proudcloud/clouduino/docs/images/preferences.png

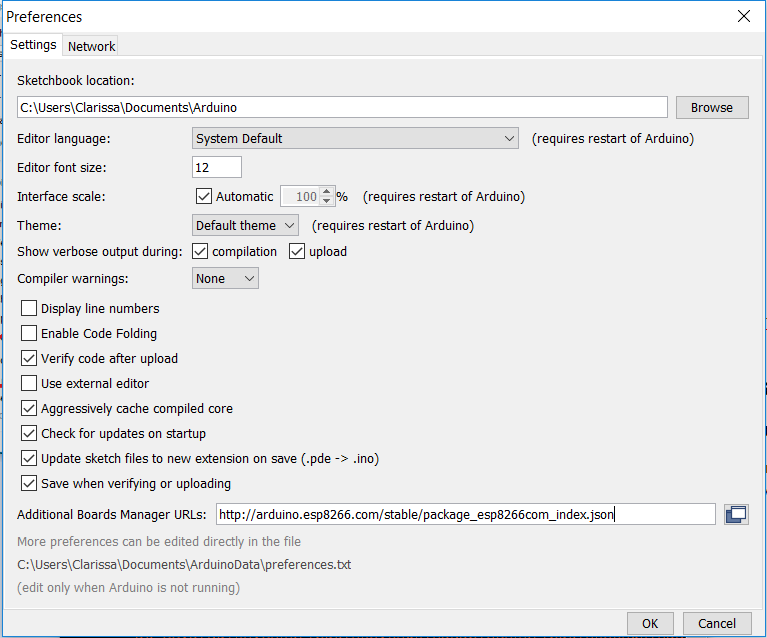
docs/images/preferences.png
