proudcloud/clouduino/example/Webserver_example/Clouduino_Webserver_LEDs_fritzing_Breadboard.PNG

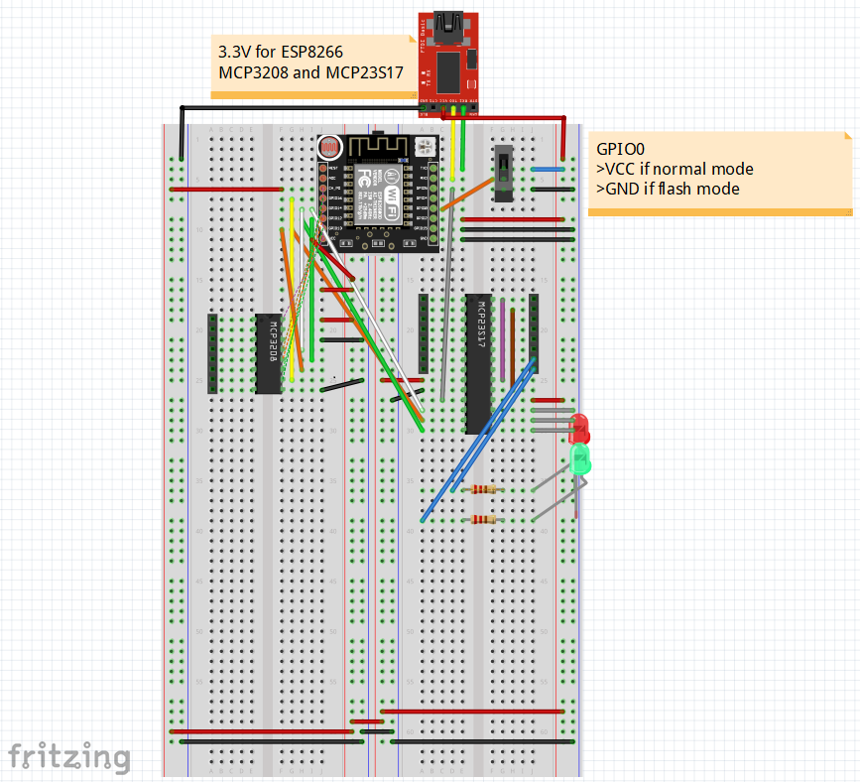
example/Webserver_example/Clouduino_Webserver_LEDs_fritzing_Breadboard.PNG
