proudcloud/clouduino/example/Webserver_example/Clouduino_Webserver_LEDs_fritzing_Schem.PNG

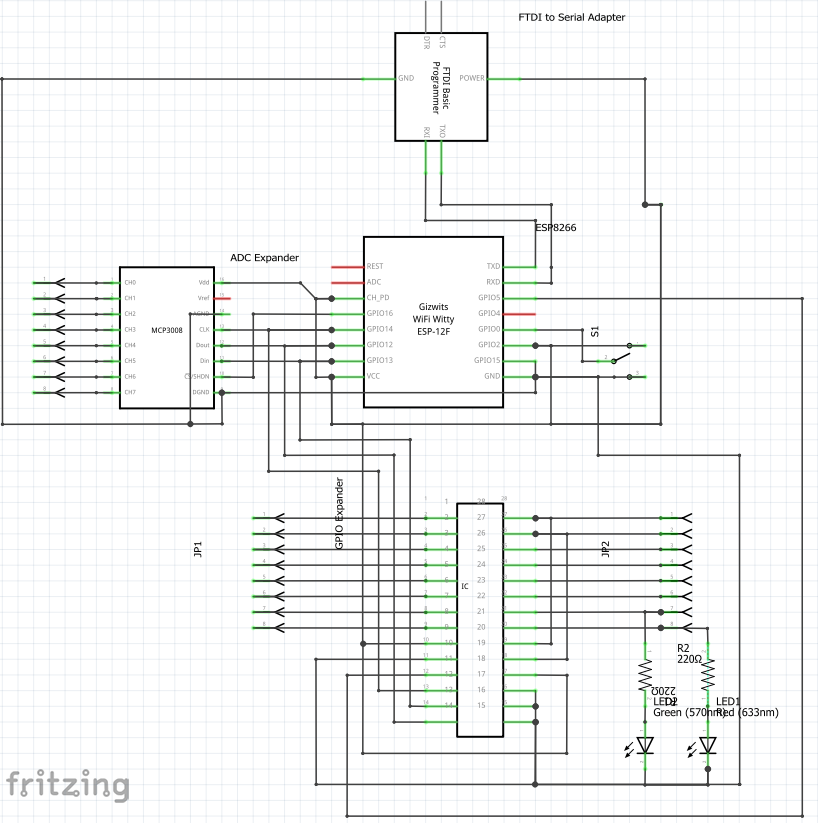
example/Webserver_example/Clouduino_Webserver_LEDs_fritzing_Schem.PNG
