proudcloud/clouduino/example/ADC_example/ADC_test_LDR fritzing_Schem.PNG

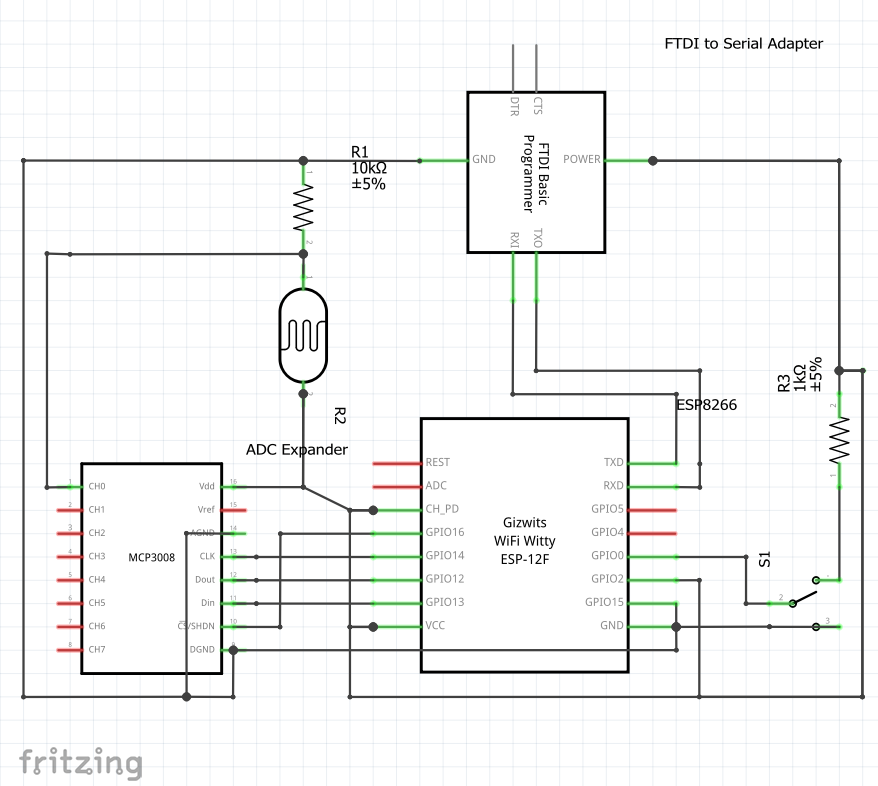
example/ADC_example/ADC_test_LDR fritzing_Schem.PNG
