proudcloud/clouduino/example/ADC_example/ADC_test_LDR/ADC_test_LDR.ino

/**
 * Basic ADC reading example.
 * - connects to ADC
 * - reads value from channel
 * - converts value to analog voltage
 */

#include <SPI.h>
#include <Mcp3208.h>

#define SPI_CS    	16 		   // SPI slave select: GPIO16 pin of ESP8266
#define ADC_VREF    3300     // 3.3V Vref
#define ADC_CLK     1600000  // SPI clock 1.6MHz


MCP3208 adc(ADC_VREF, SPI_CS);

void setup() {

  // configure PIN mode
  pinMode(SPI_CS, OUTPUT);

  // set initial PIN state
  digitalWrite(SPI_CS, HIGH);

  // initialize serial
  Serial.begin(115200);     

  // initialize SPI interface for MCP3208
	SPISettings settings(ADC_CLK, MSBFIRST, SPI_MODE0); 
  SPI.begin();
  SPI.beginTransaction(settings);
}

void loop() {

  uint32_t t1;
	uint32_t t2;

  // start sampling
  Serial.println("Reading...");

  t1 = micros();
  uint16_t raw = adc.read(MCP3208::SINGLE_0); //Read Single channel 0 of MCP3208 
	t2 = micros();

  // get analog value
  uint16_t val = adc.toAnalog(raw);

//// Read from the output using Serial monitor at 115200 baud rate.
  // readed value
  Serial.print("value: ");
  Serial.print(raw);
  Serial.print(" (");
  Serial.print(val);
  Serial.println(" mV)");

  // sampling time
  Serial.print("Sampling time: ");
	Serial.print(static_cast<double>(t2 - t1) / 1000, 4);
  Serial.println("ms");

  delay(1000);
}
